ahpohl/gasmeter/src/Gasmeter.cpp

#include "Gasmeter.h"
#include <charconv>
#include <chrono>
#include <cstring>
#include <iomanip>
#include <iostream>
#include <stdexcept>
#include <thread>
#include <unistd.h>
#include <vector>

const std::set<std::string> Gasmeter::ValidKeys{
    "mqtt_broker", "mqtt_password", "mqtt_port",     "mqtt_topic", "mqtt_user",
    "mqtt_cafile", "mqtt_capath",   "serial_device", "gas_rate",   "gas_price",
    "gas_factor",  "gas_meter",     "gas_force",     "log_level",  "level_low",
    "level_high",  "raw_mode"};

Gasmeter::Gasmeter(void) : Log(false), RawMode(false) {
  Cfg = new GasmeterConfig();
  Firmware = new GasmeterFirmware();
  Mqtt = new GasmeterMqtt();
}

Gasmeter::~Gasmeter(void) {
  if (Mqtt->GetConnectStatus()) {
    Mqtt->PublishMessage("offline", Cfg->GetValue("mqtt_topic") + "/status", 1,
                         true);
    std::this_thread::sleep_for(std::chrono::milliseconds(1));
  }
  if (Mqtt) {
    delete Mqtt;
  }
  if (Firmware) {
    delete Firmware;
  }
  if (Cfg) {
    delete Cfg;
  };
}

bool Gasmeter::Setup(const std::string &config) {
  if (!Cfg->Begin(config)) {
    ErrorMessage = Cfg->GetErrorMessage();
    return false;
  }
  if (!Cfg->ValidateKeys(Gasmeter::ValidKeys)) {
    ErrorMessage = Cfg->GetErrorMessage();
    return false;
  }
  this->SetLogLevel();
  if (Log & static_cast<unsigned char>(LogLevel::CONFIG)) {
    Cfg->ShowConfig();
  }
  if (!(Cfg->KeyExists("serial_device"))) {
    ErrorMessage = Cfg->GetErrorMessage();
    return false;
  }
  if (!(Cfg->KeyExists("mqtt_broker"))) {
    ErrorMessage = Cfg->GetErrorMessage();
    return false;
  }
  if (!(Cfg->KeyExists("mqtt_topic"))) {
    ErrorMessage = Cfg->GetErrorMessage();
    return false;
  }
  if (!(Cfg->KeyExists("gas_rate"))) {
    ErrorMessage = Cfg->GetErrorMessage();
    return false;
  }
  if (!(Cfg->KeyExists("gas_price"))) {
    ErrorMessage = Cfg->GetErrorMessage();
    return false;
  }
  if (!(Cfg->KeyExists("gas_factor"))) {
    ErrorMessage = Cfg->GetErrorMessage();
    return false;
  }
  if (!(Cfg->KeyExists("gas_meter"))) {
    ErrorMessage = Cfg->GetErrorMessage();
    return false;
  }
  if (Cfg->KeyExists("raw_mode") &&
      (StringTo<bool>(Cfg->GetValue("raw_mode")))) {
    RawMode = true;
  }

  if (!Firmware->Setup(Cfg->GetValue("serial_device"))) {
    ErrorMessage = Firmware->GetErrorMessage();
    return false;
  }
  if (Log & static_cast<unsigned char>(LogLevel::FIRMWARE)) {
    Firmware->SetDebug(true);
  }
  if (StringTo<bool>(Cfg->GetValue("gas_force"))) {
    if (!Firmware->ClearMeterVolume()) {
      ErrorMessage = Firmware->GetErrorMessage();
      return false;
    }
  }
  if (!Firmware->SetMeterVolume(StringTo<float>(Cfg->GetValue("gas_meter")))) {
    ErrorMessage = Firmware->GetErrorMessage();
    return false;
  }
  if (!Firmware->SetThresholdLevels(
          StringTo<short int>(Cfg->GetValue("level_low")),
          StringTo<short int>(Cfg->GetValue("level_high")))) {
    ErrorMessage = Firmware->GetErrorMessage();
    return false;
  }
  if (!Firmware->ReadDspValue(GasData.Volume,
                              GasmeterFirmware::DspValue::GAS_VOLUME)) {
    ErrorMessage = Firmware->GetErrorMessage();
    return false;
  }
  std::cout << "Current meter reading: " << GasData.Volume << " m³"
            << std::endl;

  if (!Mqtt->Begin()) {
    ErrorMessage = Mqtt->GetErrorMessage();
    return false;
  }
  if (Log & static_cast<unsigned char>(LogLevel::MQTT)) {
    Mqtt->SetDebug(true);
  }
  if ((Cfg->KeyExists("mqtt_user") && Cfg->KeyExists("mqtt_password"))) {
    if (!Mqtt->SetUserPassAuth(Cfg->GetValue("mqtt_user"),
                               Cfg->GetValue("mqtt_password"))) {
      ErrorMessage = Mqtt->GetErrorMessage();
      return false;
    }
  }
  if (Cfg->KeyExists("mqtt_cafile") || Cfg->KeyExists("mqtt_capath")) {
    if (!Mqtt->SetTlsConnection(Cfg->GetValue("mqtt_cafile"),
                                Cfg->GetValue("mqtt_capath"))) {
      ErrorMessage = Mqtt->GetErrorMessage();
      return false;
    }
  }
  if (Cfg->KeyExists("mqtt_port")) {
    if (!Mqtt->Connect(Cfg->GetValue("mqtt_broker"),
                       StringTo<int>(Cfg->GetValue("mqtt_port")), 60)) {
      ErrorMessage = Mqtt->GetErrorMessage();
      return false;
    }
  } else {
    if (!Mqtt->Connect(Cfg->GetValue("mqtt_broker"), 1883, 60)) {
      ErrorMessage = Mqtt->GetErrorMessage();
      return false;
    }
  }
  if (!Mqtt->SetLastWillTestament(
          "offline", Cfg->GetValue("mqtt_topic") + "/status", 1, true)) {
    ErrorMessage = Mqtt->GetErrorMessage();
    return false;
  }

  return true;
}

bool Gasmeter::Receive(void) {
  if (!Firmware->ReadDspValue(GasData.Volume,
                              GasmeterFirmware::DspValue::GAS_VOLUME)) {
    ErrorMessage = Firmware->GetErrorMessage();
    return false;
  }
  if (RawMode) {
    if (!Firmware->ReadDspValue(GasData.RawIr,
                                GasmeterFirmware::DspValue::RAW_IR)) {
      ErrorMessage = Firmware->GetErrorMessage();
      return false;
    }
    std::cout << (GasData.RawIr * 100) << " " << GasData.Volume << std::endl;
  }

  return true;
}

bool Gasmeter::Publish(void) {
  unsigned long long now =
      std::chrono::duration_cast<std::chrono::milliseconds>(
          std::chrono::high_resolution_clock::now().time_since_epoch())
          .count();

  std::ios::fmtflags old_settings = Payload.flags();
  Payload.str(std::string());
  Payload.setf(std::ios::fixed, std::ios::floatfield);

  Payload << "{"
          << "\"time\":" << now << ","
          << "\"volume\":" << std::setprecision(2) << GasData.Volume << ","
          << "\"state\":" << (GetState(GasData.Volume) ? "1" : "0") << ","
          << "\"rate\":" << Cfg->GetValue("gas_rate") << ","
          << "\"price\":" << Cfg->GetValue("gas_price") << ","
          << "\"factor\":" << Cfg->GetValue("gas_factor") << "}";

  if (Mqtt->GetNotifyOnlineFlag()) {
    std::cout << "Gasmeter is online." << std::endl;
    if (!Mqtt->PublishMessage("online", Cfg->GetValue("mqtt_topic") + "/status",
                              1, true)) {
      ErrorMessage = Mqtt->GetErrorMessage();
      return false;
    }
    Mqtt->SetNotifyOnlineFlag(false);
  }

  if (Mqtt->GetConnectStatus()) {
    if (!(Mqtt->PublishMessage(
            Payload.str(), Cfg->GetValue("mqtt_topic") + "/live", 0, false))) {
      ErrorMessage = Mqtt->GetErrorMessage();
      return false;
    }
  }

  if (Log & static_cast<unsigned char>(LogLevel::JSON)) {
    std::cout << Payload.str() << std::endl;
  }
  Payload.flags(old_settings);

  return true;
}

std::string Gasmeter::GetErrorMessage(void) const { return ErrorMessage; }
std::string Gasmeter::GetPayload(void) const { return Payload.str(); }

bool Gasmeter::GetState(float &current_volume) const {
  static float previous_volume = current_volume;
  bool flame_on = ((current_volume - previous_volume) > 0) ? true : false;
  previous_volume = current_volume;

  return flame_on;
}

bool Gasmeter::IsRawMode(void) const { return RawMode; }

template <typename T> T Gasmeter::StringTo(const std::string &str) const {
  T value;
  std::istringstream iss(str);
  iss >> value;
  if (iss.fail()) {
    return T();
  }
  return value;
}

void Gasmeter::SetLogLevel(void) {
  if (Cfg->KeyExists("log_level")) {
    std::string line = Cfg->GetValue("log_level");
    std::istringstream iss(line);
    std::string token;
    std::vector<std::string> log_level;

    while (std::getline(iss, token, ',')) {
      log_level.push_back(token);
    }
    for (auto it = log_level.cbegin(); it != log_level.cend(); ++it) {
      if (!(*it).compare("config")) {
        Log |= static_cast<unsigned char>(LogLevel::CONFIG);
      } else if (!(*it).compare("json")) {
        Log |= static_cast<unsigned char>(LogLevel::JSON);
      } else if (!(*it).compare("mqtt")) {
        Log |= static_cast<unsigned char>(LogLevel::MQTT);
      } else if (!(*it).compare("firmware")) {
        Log |= static_cast<unsigned char>(LogLevel::FIRMWARE);
      }
    }
  } else {
    Log = 0;
  }
}
